gabemake/fpaa_badge/esp32_sw/FPAA_ESP_IDF/src/sdcard.c

#include "sdcard.h"
static const char *TAG = "sdcard";

#ifdef USE_SD_CARD

esp_err_t mount_storage(const char* base_path)
{
    ESP_LOGI(TAG, "Initializing SD card");

    esp_vfs_fat_sdmmc_mount_config_t mount_config = {
        .format_if_mount_failed = false,
        .max_files = 5,
        .allocation_unit_size = 16 * 1024
    };
    esp_err_t ret;
    sdmmc_card_t* card;
#ifdef USE_SDMMC_MODE

    ESP_LOGI(TAG, "Using SDMMC peripheral");
    sdmmc_host_t host = SDMMC_HOST_DEFAULT();

    host.set_card_clk = 
    // This initializes the slot without card detect (CD) and write protect (WP) signals.
    // Modify slot_config.gpio_cd and slot_config.gpio_wp if your board has these signals.
    sdmmc_slot_config_t slot_config = SDMMC_SLOT_CONFIG_DEFAULT();

    // To use 1-line SD mode, change this to 1:
    slot_config.width = 1;

    // For chips which support GPIO Matrix for SDMMC peripheral, specify the pins.
    slot_config.clk = SDMMC_CLK_PIN;
    slot_config.cmd = SDMMC_CMD_PIN;
    slot_config.d0 = SDMMC_D0_PIN;
    slot_config.d1 = SDMMC_D1_PIN;
    slot_config.d2 = SDMMC_D2_PIN;
    slot_config.d3 = SDMMC_D3_PIN;

    // Enable internal pullups on enabled pins. The internal pullups
    // are insufficient however, please make sure 10k external pullups are
    // connected on the bus. This is for debug / example purpose only.
    //slot_config.flags |= SDMMC_SLOT_FLAG_INTERNAL_PULLUP;

    ret = esp_vfs_fat_sdmmc_mount(base_path, &host, &slot_config, &mount_config, &card);

#else // CONFIG_EXAMPLE_USE_SDMMC_HOST

    ESP_LOGI(TAG, "Using SPI peripheral");

    sdmmc_host_t host = SDSPI_HOST_DEFAULT();
    spi_bus_config_t bus_cfg = {
        .mosi_io_num = SDMMC_CMD_PIN,
        .miso_io_num = SDMMC_D0_PIN,
        .sclk_io_num = SDMMC_CLK_PIN,
        .quadwp_io_num = -1,
        .quadhd_io_num = -1,
        .max_transfer_sz = 4000,
    };

    ret = spi_bus_initialize(host.slot, &bus_cfg, SDSPI_DEFAULT_DMA);
    if (ret != ESP_OK) {
        ESP_LOGE(TAG, "Failed to initialize bus.");
        return ret;
    }

    // This initializes the slot without card detect (CD) and write protect (WP) signals.
    // Modify slot_config.gpio_cd and slot_config.gpio_wp if your board has these signals.
    sdspi_device_config_t slot_config = SDSPI_DEVICE_CONFIG_DEFAULT();
    slot_config.gpio_cs = SDMMC_D3_PIN;
    slot_config.host_id = host.slot;
    ret = esp_vfs_fat_sdspi_mount(base_path, &host, &slot_config, &mount_config, &card);

#endif // !CONFIG_EXAMPLE_USE_SDMMC_HOST

    if (ret != ESP_OK){
        if (ret == ESP_FAIL) {
            ESP_LOGE(TAG, "Failed to mount filesystem. "
                "If you want the card to be formatted, set the EXAMPLE_FORMAT_IF_MOUNT_FAILED menuconfig option.");
        } else {
            ESP_LOGE(TAG, "Failed to initialize the card (%s). "
                "Make sure SD card lines have pull-up resistors in place.", esp_err_to_name(ret));
        }
        return ret;
    }

    sdmmc_card_print_info(stdout, card);
    return ESP_OK;
}

#else // not USE_SD_CARD

/* Function to initialize SPIFFS */
esp_err_t mount_storage(const char* base_path)
{
    ESP_LOGI(TAG, "Initializing SPIFFS");

    esp_vfs_spiffs_conf_t conf = {
        .base_path = base_path,
        .partition_label = NULL,
        .max_files = 5,   // This sets the maximum number of files that can be open at the same time
        .format_if_mount_failed = true
    };

    esp_err_t ret = esp_vfs_spiffs_register(&conf);
    if (ret != ESP_OK) {
        if (ret == ESP_FAIL) {
            ESP_LOGE(TAG, "Failed to mount or format filesystem");
        } else if (ret == ESP_ERR_NOT_FOUND) {
            ESP_LOGE(TAG, "Failed to find SPIFFS partition");
        } else {
            ESP_LOGE(TAG, "Failed to initialize SPIFFS (%s)", esp_err_to_name(ret));
        }
        return ret;
    }

    size_t total = 0, used = 0;
    ret = esp_spiffs_info(NULL, &total, &used);
    if (ret != ESP_OK) {
        ESP_LOGE(TAG, "Failed to get SPIFFS partition information (%s)", esp_err_to_name(ret));
        return ret;
    }

    ESP_LOGI(TAG, "Partition size: total: %d, used: %d", total, used);
    return ESP_OK;
}

#endif // !USE_SD_CARD
