gabemake/fpaa_badge/esp32_sw/FPAA_ESP_IDF/src/wifi.c

#include "wifi.h"

static const char *TAG = "wifi softAP";

static void wifi_event_handler(void* arg, esp_event_base_t event_base,
                                    int32_t event_id, void* event_data)
{
    if (event_id == WIFI_EVENT_AP_STACONNECTED) {
        wifi_event_ap_staconnected_t* event = (wifi_event_ap_staconnected_t*) event_data;
        ESP_LOGI(TAG, "station "MACSTR" join, AID=%d",
                 MAC2STR(event->mac), event->aid);
    } else if (event_id == WIFI_EVENT_AP_STADISCONNECTED) {
        wifi_event_ap_stadisconnected_t* event = (wifi_event_ap_stadisconnected_t*) event_data;
        ESP_LOGI(TAG, "station "MACSTR" leave, AID=%d",
                 MAC2STR(event->mac), event->aid);
    }
}

void wifi_init_softap(void)
{

    ESP_ERROR_CHECK(esp_netif_init());
    ESP_ERROR_CHECK(esp_event_loop_create_default());
    esp_netif_create_default_wifi_ap();

    wifi_init_config_t cfg = WIFI_INIT_CONFIG_DEFAULT();
    ESP_ERROR_CHECK(esp_wifi_init(&cfg));

    ESP_ERROR_CHECK(esp_event_handler_instance_register(WIFI_EVENT,
                                                        ESP_EVENT_ANY_ID,
                                                        &wifi_event_handler,
                                                        NULL,
                                                        NULL));


    wifi_config_t wifi_config = {
        .ap = {
            .ssid = BADGE_ESP_WIFI_SSID,
            .ssid_len = strlen(BADGE_ESP_WIFI_SSID),
            .channel = BADGE_ESP_WIFI_CHANNEL,
            .password = BADGE_ESP_WIFI_PASS,
            .max_connection = BADGE_MAX_STA_CONN,
#ifdef CONFIG_ESP_WIFI_SOFTAP_SAE_SUPPORT
            .authmode = WIFI_AUTH_WPA3_PSK,
            .sae_pwe_h2e = WPA3_SAE_PWE_BOTH,
#else /* CONFIG_ESP_WIFI_SOFTAP_SAE_SUPPORT */
            .authmode = WIFI_AUTH_WPA2_PSK,
#endif
            .pmf_cfg = {
                    .required = true,
            },
        },
    };
    if (strlen(BADGE_ESP_WIFI_PASS) == 0) {
        wifi_config.ap.authmode = WIFI_AUTH_OPEN;
    }

    ESP_ERROR_CHECK(esp_wifi_set_mode(WIFI_MODE_AP));
    ESP_ERROR_CHECK(esp_wifi_set_config(WIFI_IF_AP, &wifi_config));
    ESP_ERROR_CHECK(esp_wifi_start());


    ESP_LOGI(TAG, "wifi_init_softap finished. SSID:%s password:%s channel:%d",
             BADGE_ESP_WIFI_SSID, BADGE_ESP_WIFI_PASS, BADGE_ESP_WIFI_CHANNEL);
}
